sanujkul/KALAM_Canast_2019/Old Git Repo/BAGS/Eagle/Container/Cansat2019_1516_Container_v02.brd

## EAGLE design Old Git Repo/BAGS/Eagle/Container/Cansat2019_1516_Container_v02.brd (2019-06-20, an earlier design)

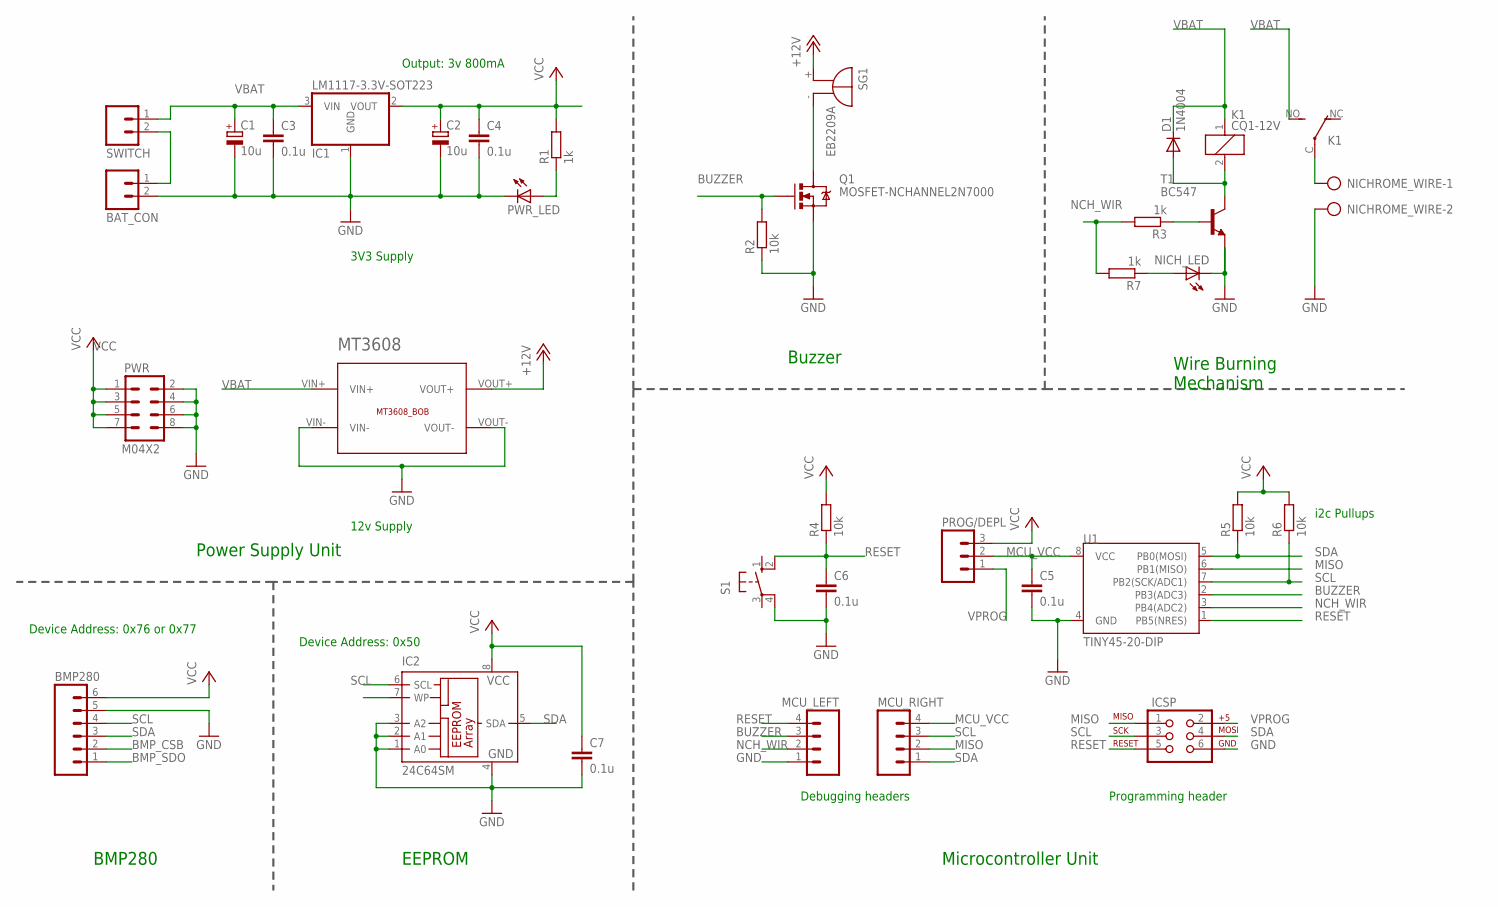
[picture p47: schematic Cansat2019_1516_Container_v02.sch]

Parts:
BAT_CON: M02; 02P
BMP280: M06; 06P
C1, C2: 10u; E2,5-6
C3, C4, C5, C6, C7: 0.1u; C025-025X050
D1: 1N4004; DO41-10
IC1: LM1117-3.3V-SOT223; SOT223
IC2: 24C64SM; SO-08M
ICSP: AVR_SPI_PRG_6NS; 2X3-NS
K1: CQ1-12V; CQ1
MCU_LEFT: M04; 04P
MCU_RIGHT: M04; 04P
MT3608: MT3608_BOB
NICHROME_WIRE: AK500/2-H
NICH_LED: LED3MM
PROG/DEPL: M03PTH; 1X03
PWR: M04X2; 2X4
PWR_LED: LED3MM
Q1: MOSFET-NCHANNEL2N7000; TO-92
R1, R3, R7: 1k; 0204/7
R2, R4, R5, R6: 10k; 0204/7
S1: PUSH-BUTTON-6MM; B3F-10XX
SG1: EB2209A
SWITCH: M02; 02P
T1: BC547; TO92
U1: TINY45-20-DIP; DIP08

Connections:
+12V: MT3608.VOUT+, SG1.+
BMP_CSB: BMP280.2
BMP_SDO: BMP280.1
BUZZER: MCU_LEFT.3, Q1.2 (G), R2.2, U1.2 (PB3(ADC3))
GND: BAT_CON.2, BMP280.5, C1.-, C2.-, C3.2, C4.2, C5.2, C6.2, C7.2, IC1.1 (GND), IC2.1 (A0), IC2.2 (A1), IC2.3 (A2), IC2.4 (GND), ICSP.6, MCU_LEFT.1, MT3608.VIN-, MT3608.VOUT-, NICHROME_WIRE.2, NICH_LED.K (C), PWR.2, PWR.4, PWR.6, PWR.8, PWR_LED.K (C), Q1.1 (S), R2.1, S1.4 (P1), U1.4 (GND)
MCU_VCC: C5.1, MCU_RIGHT.4, PROG/DEPL.2, U1.8 (VCC)
MISO: ICSP.1, MCU_RIGHT.2, U1.6 (PB1(MISO))
unnamed: Q1.3 (D), SG1.-
unnamed: K1.C, NICHROME_WIRE.1
unnamed: PWR_LED.A, R1.1
unnamed: R3.1, T1.2 (B)
unnamed: NICH_LED.A, R7.1
unnamed: BAT_CON.1, SWITCH.2
unnamed: D1.A, K1.2, T1.3 (C)
NCH_WIR: MCU_LEFT.2, R3.2, R7.2, U1.3 (PB4(ADC2))
RESET: C6.1, ICSP.5, MCU_LEFT.4, R4.1, S1.2 (S1), U1.1 (PB5(NRES))
SCL: BMP280.4, IC2.6 (SCL), ICSP.3, MCU_RIGHT.3, R6.1, U1.7 (PB2(SCK/ADC1))
SDA: BMP280.3, IC2.5 (SDA), ICSP.4, MCU_RIGHT.1, R5.1, U1.5 (PB0(MOSI))
VBAT: C1.+, C3.1, D1.C, IC1.3 (VIN), K1.1, K1.NO (S), MT3608.VIN+, SWITCH.1
VCC: BMP280.6, C2.+, C4.1, C7.1, IC1.2 (VOUT), IC2.8 (VCC), PROG/DEPL.3, PWR.1, PWR.3, PWR.5, PWR.7, R1.2, R4.2, R5.2, R6.2
VPROG: ICSP.2, PROG/DEPL.1

Notes on the sheet:
Power Supply Unit
Buzzer
Wire Burning Mechanism
Debugging headers
Programming header
Microcontroller Unit
3V3 Supply
12v Supply
BMP280
i2c Pullups
Output: 3v 800mA
Device Address: 0x50
EEPROM
Device Address: 0x76 or 0x77
