sanujkul/KALAM_Canast_2019/Old Git Repo/BAGS/Eagle/Container/Cansat2019_1516_Container_v02.brd

## EAGLE design Old Git Repo/BAGS/Eagle/Container/Cansat2019_1516_Container_v02.brd (continued)

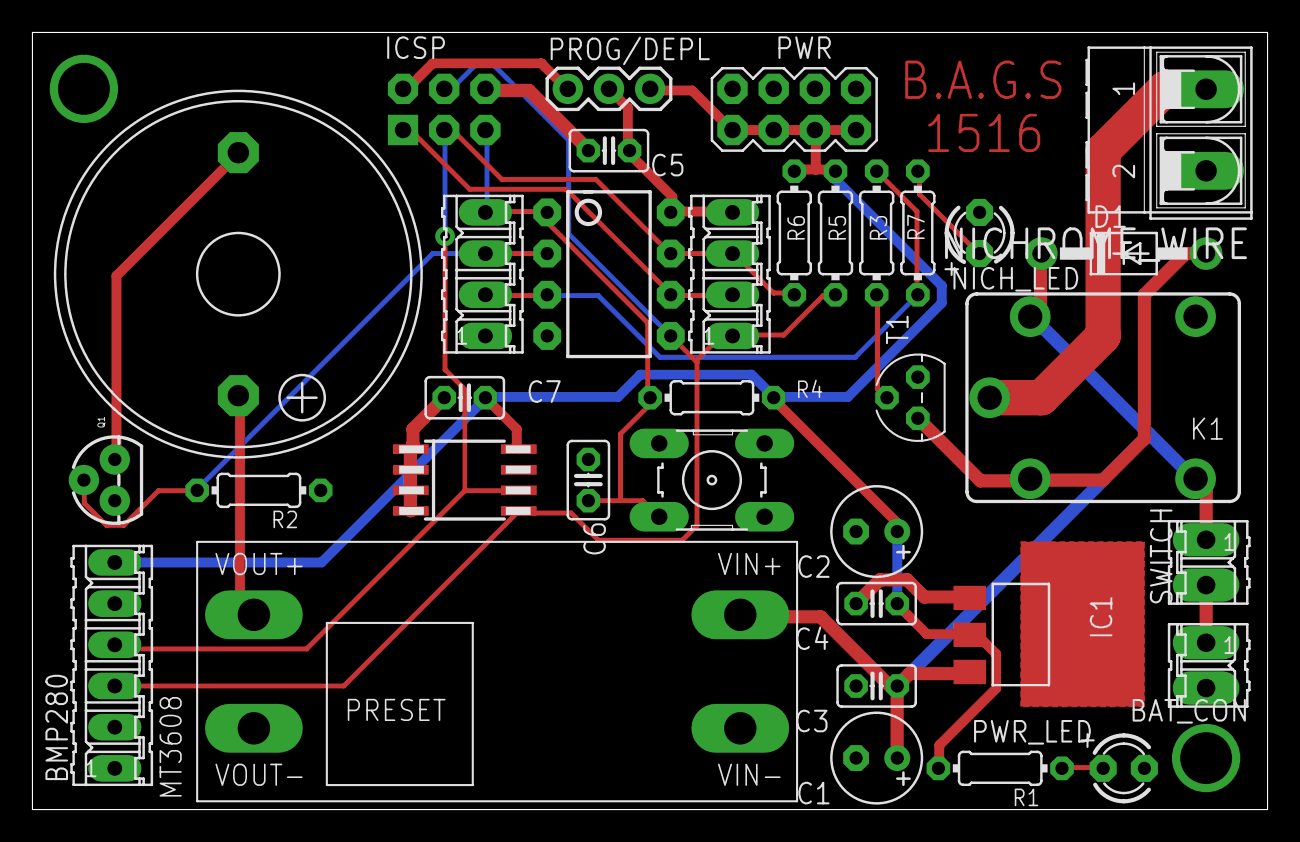
[picture p48: board Cansat2019_1516_Container_v02.brd from above]

Board: 2 copper layers, 76.2 x 47.9 mm, 35 parts (0 on the bottom side), 19 nets.
