sanujkul/KALAM_Canast_2019/Old Git Repo/KALAM/EAGLE/Container/Cansat2019_3279_Container_v03.brd

## EAGLE design Old Git Repo/KALAM/EAGLE/Container/Cansat2019_3279_Container_v03.brd (2019-06-20, an earlier design)

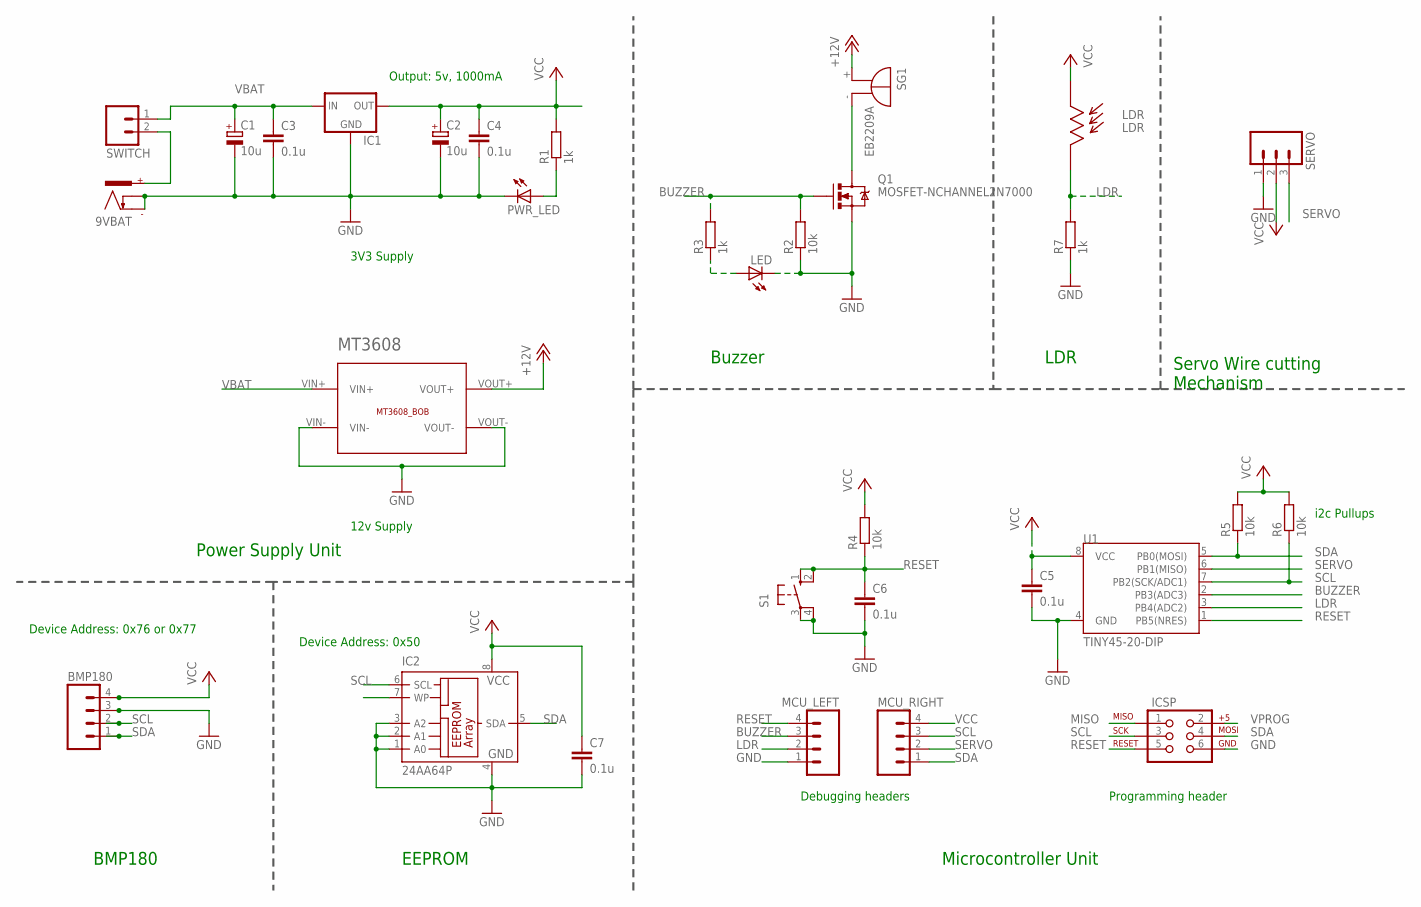
[picture p49: schematic Cansat2019_3279_Container_v03.sch]

Parts:
9VBAT: POWER_CON; NEB21R
BMP180: M04; 04P
C1, C2: 10u; E2,5-6
C3, C4, C5, C6, C7: 0.1u; C025-025X050
IC1: V_REG_78XX-TO-220; TO-220-ALT
IC2: 24AA64P; DIL8
ICSP: AVR_SPI_PRG_6NS; 2X3-NS
LDR: LDR; LDR-5MM
LED: LED3MM
MCU_LEFT: M04; 04P
MCU_RIGHT: M04; 04P
MT3608: MT3608_BOB
PWR_LED: LED3MM
Q1: MOSFET-NCHANNEL2N7000; TO-92
R1, R3, R7: 1k; 0204/7
R2, R4, R5, R6: 10k; 0204/7
S1: PUSH-BUTTON-6MM; B3F-10XX
SERVO: M03; 03P
SG1: EB2209A
SWITCH: M02; 02P
U1: TINY45-20-DIP; DIP08

Connections:
+12V: MT3608.VOUT+, SG1.+
BUZZER: MCU_LEFT.3, Q1.2 (G), R2.2, R3.2, U1.2 (PB3(ADC3))
GND: 9VBAT.-, 9VBAT.C, BMP180.3, C1.-, C2.-, C3.2, C4.2, C5.2, C6.2, C7.2, IC1.GND, IC2.1 (A0), IC2.2 (A1), IC2.3 (A2), IC2.4 (GND), ICSP.6, LED.K (C), MCU_LEFT.1, MT3608.VIN-, MT3608.VOUT-, PWR_LED.K (C), Q1.1 (S), R2.1, R7.1, S1.3, S1.4 (P1), SERVO.1, U1.4 (GND)
LDR: LDR.P$2, MCU_LEFT.2, R7.2, U1.3 (PB4(ADC2))
MISO: ICSP.1
unnamed: Q1.3 (D), SG1.-
unnamed: LED.A, R3.1
unnamed: PWR_LED.A, R1.1
unnamed: 9VBAT.+, SWITCH.2
RESET: C6.1, ICSP.5, MCU_LEFT.4, R4.1, S1.1 (S), S1.2 (S1), U1.1 (PB5(NRES))
SCL: BMP180.2, IC2.6 (SCL), ICSP.3, MCU_RIGHT.3, R6.1, U1.7 (PB2(SCK/ADC1))
SDA: BMP180.1, IC2.5 (SDA), ICSP.4, MCU_RIGHT.1, R5.1, U1.5 (PB0(MOSI))
SERVO: MCU_RIGHT.2, SERVO.3, U1.6 (PB1(MISO))
VBAT: C1.+, C3.1, IC1.IN, MT3608.VIN+, SWITCH.1
VCC: BMP180.4, C2.+, C4.1, C5.1, C7.1, IC1.OUT, IC2.8 (VCC), LDR.P$1, MCU_RIGHT.4, R1.2, R4.2, R5.2, R6.2, SERVO.2, U1.8 (VCC)
VPROG: ICSP.2

Notes on the sheet:
Power Supply Unit
Buzzer
Servo Wire cutting Mechanism
Debugging headers
Programming header
Microcontroller Unit
3V3 Supply
12v Supply
BMP180
i2c Pullups
Output: 5v, 1000mA
Device Address: 0x50
EEPROM
Device Address: 0x76 or 0x77
LDR

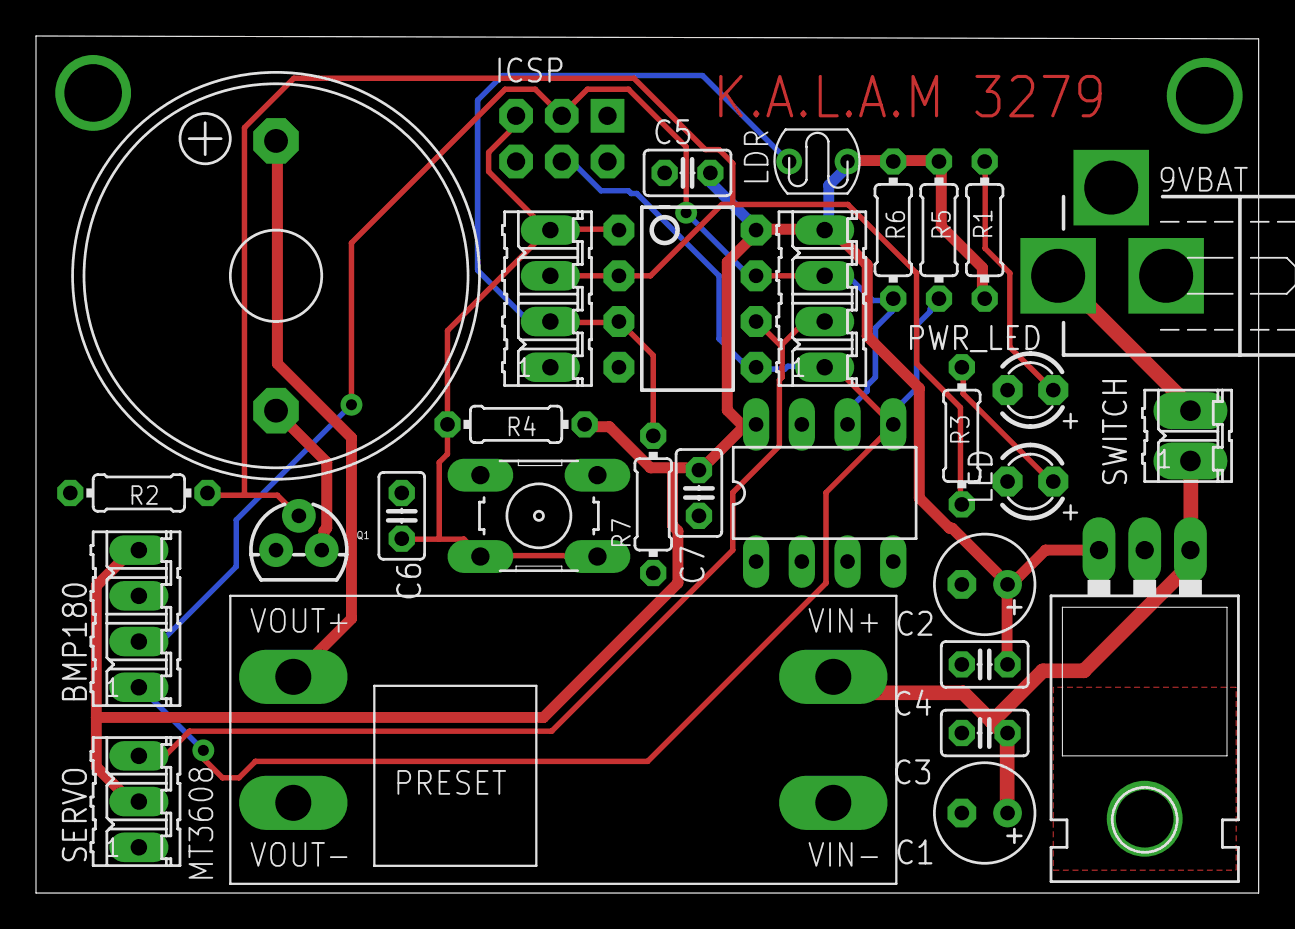
[picture p50: board Cansat2019_3279_Container_v03.brd from above]

Board: 2 copper layers, 67.9 x 47.6 mm, 31 parts (0 on the bottom side), 14 nets.
