sanujkul/KALAM_Canast_2019/Old Git Repo/KALAM/EAGLE/Container/Cansat2019_3279_Container_v04.brd

## EAGLE design Old Git Repo/KALAM/EAGLE/Container/Cansat2019_3279_Container_v04.brd (2019-06-20, an earlier design)

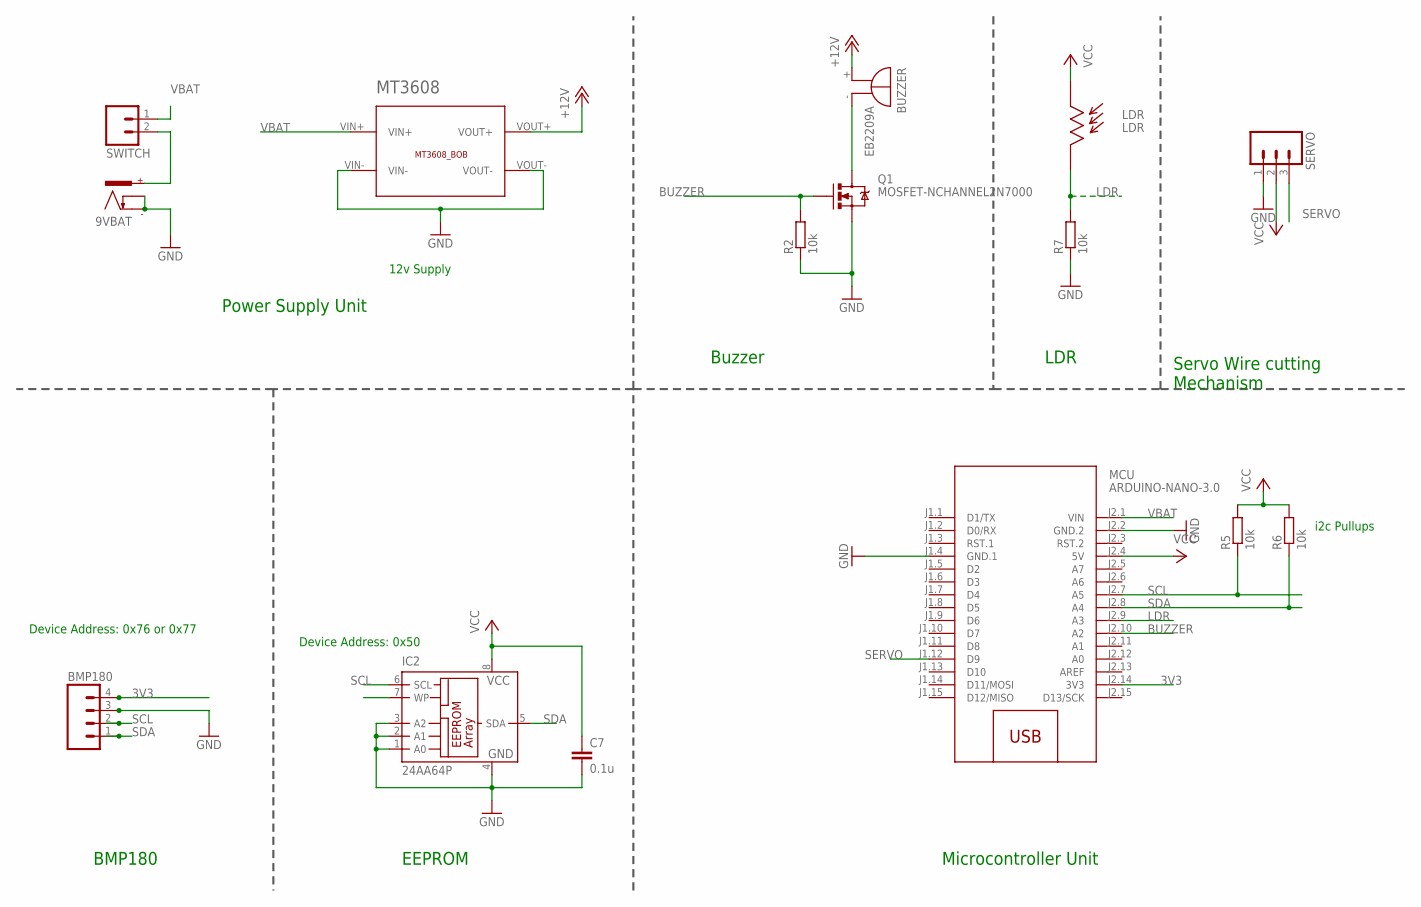
[picture p51: schematic Cansat2019_3279_Container_v04.sch]

Parts:
9VBAT: POWER_CON; NEB21R
BMP180: M04; 04P
BUZZER: EB2209A
C7: 0.1u; C025-025X050
IC2: 24AA64P; DIL8
LDR: LDR; LDR-5MM
MCU: ARDUINO-NANO-3.0
MT3608: MT3608_BOB
Q1: MOSFET-NCHANNEL2N7000; TO-92
R2, R5, R6, R7: 10k; 0204/7
SERVO: M03; 03P
SWITCH: M02; 02P

Connections:
3V3: BMP180.4, MCU.J2.14 (3V3)
+12V: BUZZER.+, MT3608.VOUT+
BUZZER: MCU.J2.10 (A2), Q1.2 (G), R2.2
GND: 9VBAT.-, 9VBAT.C, BMP180.3, C7.2, IC2.1 (A0), IC2.2 (A1), IC2.3 (A2), IC2.4 (GND), MCU.J1.4 (GND.1), MCU.J2.2 (GND.2), MT3608.VIN-, MT3608.VOUT-, Q1.1 (S), R2.1, R7.1, SERVO.1
LDR: LDR.P$2, MCU.J2.9 (A3), R7.2
unnamed: BUZZER.-, Q1.3 (D)
unnamed: 9VBAT.+, SWITCH.2
SCL: BMP180.2, IC2.6 (SCL), MCU.J2.7 (A5), R5.1
SDA: BMP180.1, IC2.5 (SDA), MCU.J2.8 (A4), R6.1
SERVO: MCU.J1.12 (D9), SERVO.3
VBAT: MCU.J2.1 (VIN), MT3608.VIN+, SWITCH.1
VCC: C7.1, IC2.8 (VCC), LDR.P$1, MCU.J2.4 (5V), R5.2, R6.2, SERVO.2

Notes on the sheet:
Power Supply Unit
Buzzer
Servo Wire cutting Mechanism
Microcontroller Unit
12v Supply
BMP180
i2c Pullups
Device Address: 0x50
EEPROM
Device Address: 0x76 or 0x77
LDR

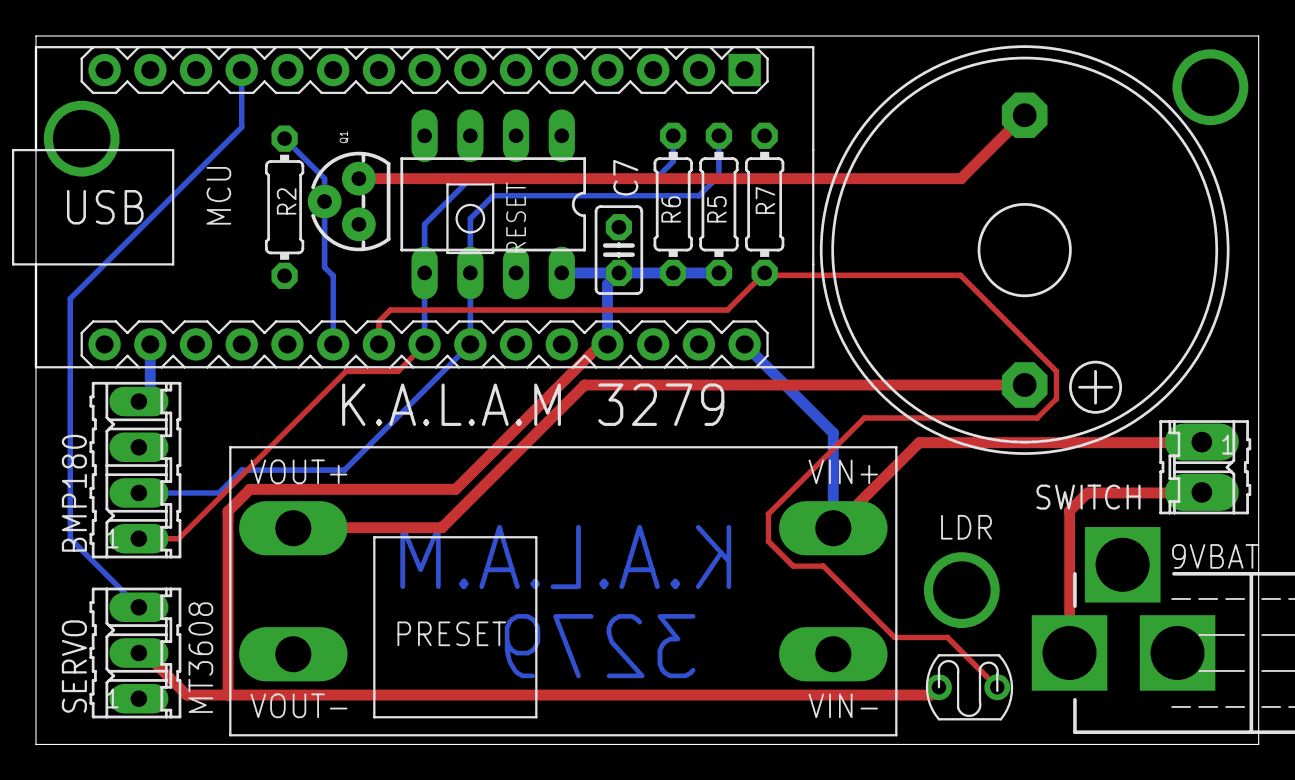
[picture p52: board Cansat2019_3279_Container_v04.brd from above]

Board: 2 copper layers, 67.9 x 39.4 mm, 15 parts (0 on the bottom side), 12 nets.
