sanujkul/KALAM_Canast_2019/Old Git Repo/KALAM/EAGLE/Container/Cansat2019_3279_Container_v05.brd

## EAGLE design Old Git Repo/KALAM/EAGLE/Container/Cansat2019_3279_Container_v05.brd (2019-06-20, an earlier design)

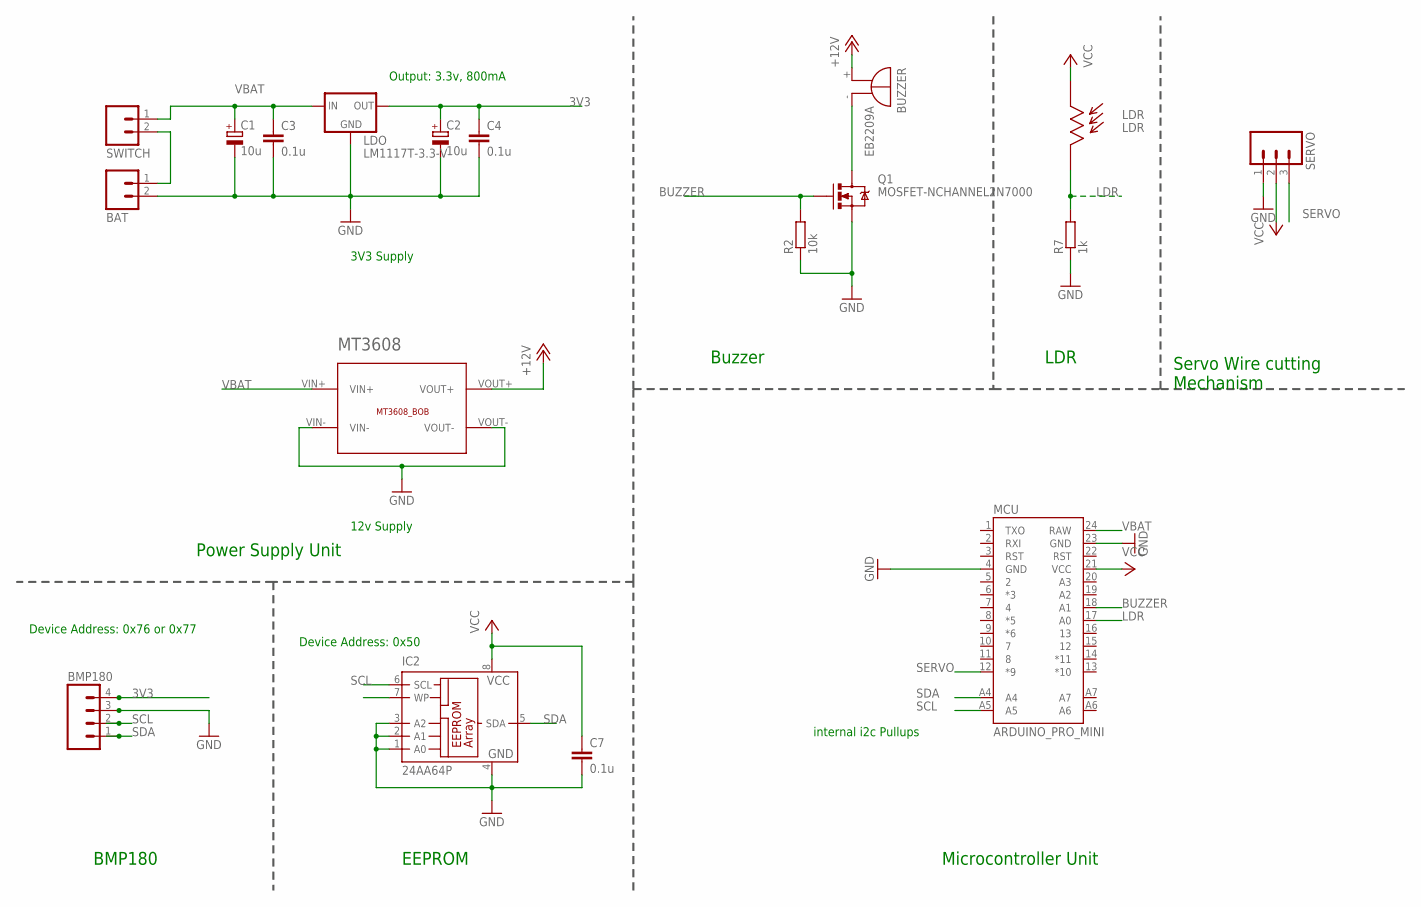
[picture p53: schematic Cansat2019_3279_Container_v05.sch]

Parts:
BAT: M02; 02P
BMP180: M04; 04P
BUZZER: EB2209A
C1, C2: 10u; E2,5-6
C3, C4, C7: 0.1u; C025-025X050
IC2: 24AA64P; DIL8
LDO: LM1117T-3.3-V; TO220V
LDR: LDR; LDR-5MM
MCU: ARDUINO_PRO_MINI
MT3608: MT3608_BOB
Q1: MOSFET-NCHANNEL2N7000; TO-92
R2: 10k; 0204/7
R7: 1k; 0204/7
SERVO: M03; 03P
SWITCH: M02; 02P

Connections:
3V3: BMP180.4, C2.+, C4.1, LDO.2 (OUT)
+12V: BUZZER.+, MT3608.VOUT+
BUZZER: MCU.18 (A1), Q1.2 (G), R2.2
GND: BAT.2, BMP180.3, C1.-, C2.-, C3.2, C4.2, C7.2, IC2.1 (A0), IC2.2 (A1), IC2.3 (A2), IC2.4 (GND), LDO.1 (GND), MCU.4 (GND), MCU.23 (GND), MT3608.VIN-, MT3608.VOUT-, Q1.1 (S), R2.1, R7.1, SERVO.1
LDR: LDR.P$2, MCU.17 (A0), R7.2
unnamed: BUZZER.-, Q1.3 (D)
unnamed: BAT.1, SWITCH.2
SCL: BMP180.2, IC2.6 (SCL), MCU.A5
SDA: BMP180.1, IC2.5 (SDA), MCU.A4
SERVO: MCU.12 (*9), SERVO.3
VBAT: C1.+, C3.1, LDO.3 (IN), MCU.24 (RAW), MT3608.VIN+, SWITCH.1
VCC: C7.1, IC2.8 (VCC), LDR.P$1, MCU.21 (VCC), SERVO.2

Notes on the sheet:
Power Supply Unit
Buzzer
Servo Wire cutting Mechanism
Microcontroller Unit
3V3 Supply
12v Supply
BMP180
Output: 3.3v, 800mA
Device Address: 0x50
EEPROM
Device Address: 0x76 or 0x77
LDR
internal i2c Pullups

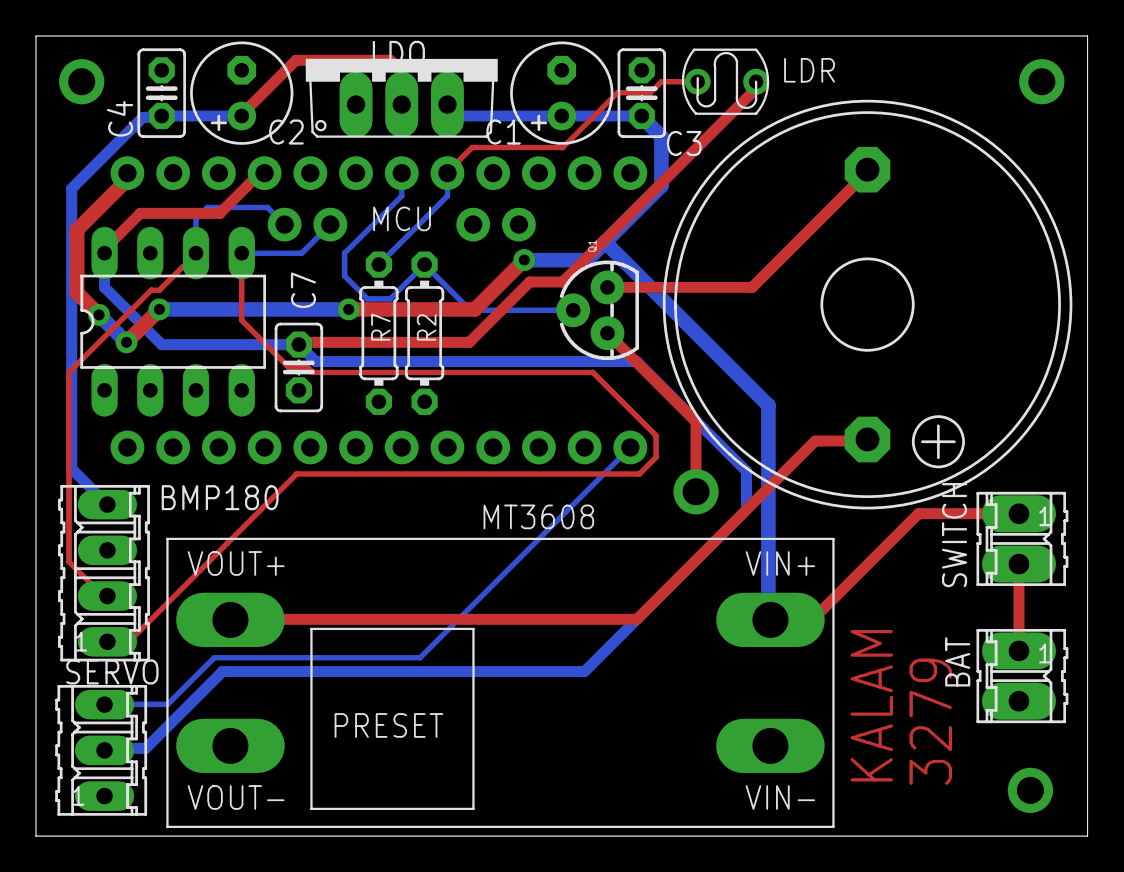
[picture p54: board Cansat2019_3279_Container_v05.brd from above]

Board: 2 copper layers, 58.4 x 44.5 mm, 18 parts (0 on the bottom side), 12 nets.
