sanujkul/KALAM_Canast_2019/Old Git Repo/KALAM/EAGLE/Payload_SectionA/PayloadV4.brd

## EAGLE design Old Git Repo/KALAM/EAGLE/Payload_SectionA/PayloadV4.brd (2019-06-20, an earlier design)

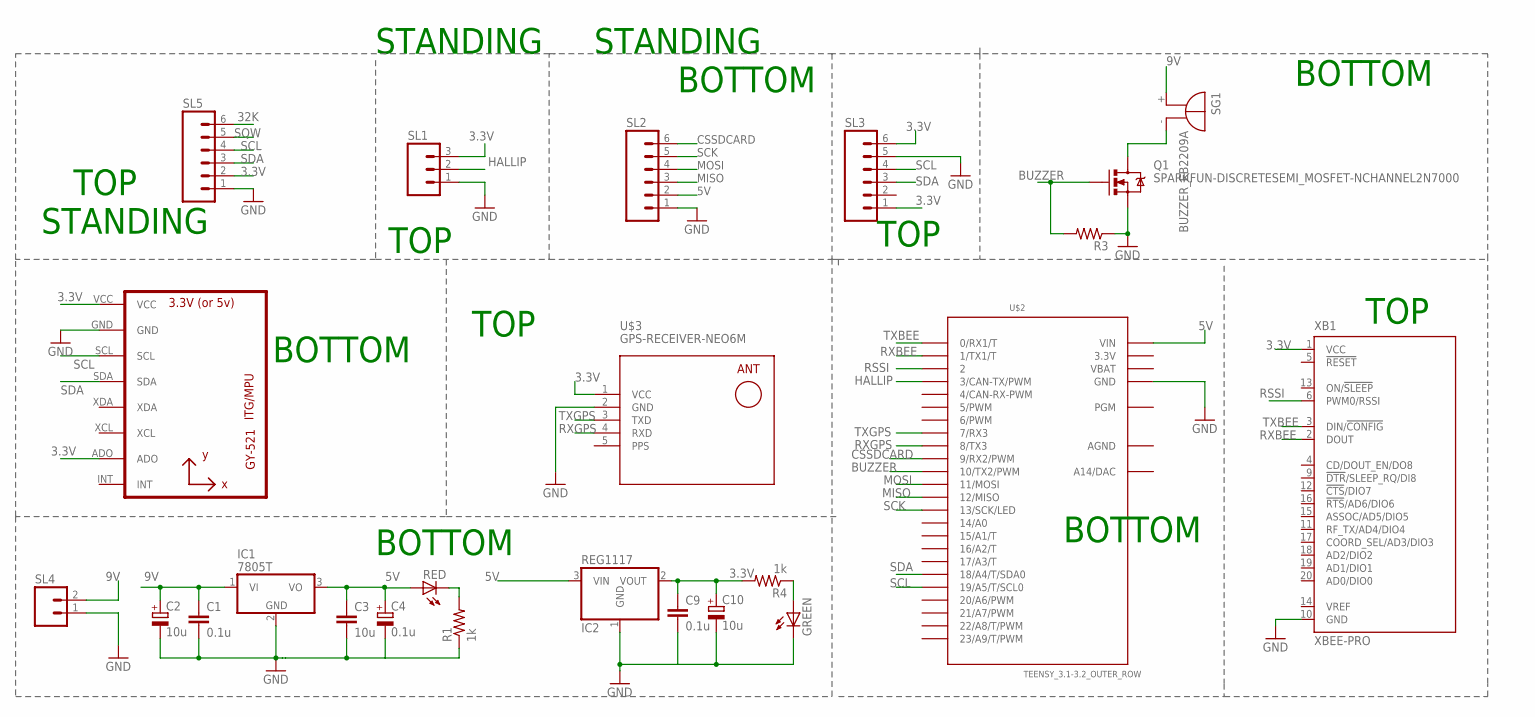
[picture p55: schematic PayloadV4.sch]

Parts:
C1, C9: 0.1u; C025-025X050
C2, C10: 10u; E2,5-6
C3: 10u; C025-025X050
C4: 0.1u; E2,5-6
GREEN: red; LED3MM
IC1: 7805T; TO220H
IC2: REG1117; SOT223
Q1: SPARKFUN-DISCRETESEMI_MOSFET-NCHANNEL2N7000; SPARKFUN-DISCRETESEMI_TO-92
R1, R4: 1k; 0204/7
R3: R-US_0204/7; 0204/7
RED: red; LED3MM
SG1: BUZZER_EB2209A
SL1: M03; 03P
SL2, SL3, SL5: M06; 06P
SL4: M02; 02P
U1: GY-521MPU6050; GY-521
U$2: TEENSY_3.1-3.2_OUTER_ROW; TEENSY_3.0-3.2&LC_OUTER_ROW
U$3: GPS-RECEIVER-NEO6M
XB1: XBEE-PRO

Connections:
3.3V: C9.1, C10.+, IC2.2 (VOUT), R4.2, SL1.3, SL3.1, SL3.6, SL5.2, U1.ADO, U1.VCC, U$2.3.3V, U$2.3.3V1 (3.3V), U$3.1 (VCC), XB1.1 (VCC)
5V: C3.1, C4.+, IC1.3 (VO), IC2.3 (VIN), RED.A, SL2.2, U$2.VIN
9V: C1.1, C2.+, IC1.1 (VI), SG1.+, SL4.2
32K: SL5.6
AGND: U$2.AGND
BUZZER: Q1.2 (G), R3.2, U$2.10 (10/TX2/PWM)
CSSDCARD: SL2.6, U$2.9 (9/RX2/PWM)
GND: C1.2, C2.-, C3.2, C4.-, C9.2, C10.-, GREEN.K (C), IC1.2 (GND), IC2.1 (GND), Q1.1 (S), R1.1, R3.1, SL1.1, SL2.1, SL3.5, SL4.1, SL5.1, U1.GND, U$2.GND, U$2.GND1 (GND), U$3.2 (GND), XB1.10 (GND)
HALLIP: SL1.2, U$2.3 (3/CAN-TX/PWM)
MISO: SL2.3, U$2.12 (12/MISO)
MOSI: SL2.4, U$2.11 (11/MOSI)
unnamed: R1.2, RED.K (C)
unnamed: GREEN.A, R4.1
unnamed: Q1.3 (D), SG1.-
PPS: U$3.5 (PPS)
RSSI: U$2.2, XB1.6 (PWM0/RSSI)
RXBEE: U$2.1 (1/TX1/T), XB1.2 (DOUT)
RXGPS: U$2.8 (8/TX3), U$3.4 (RXD)
SCK: SL2.5, U$2.13 (13/SCK/LED)
SCL: SL3.4, SL5.4, U1.SCL, U$2.19/A5 (19/A5/T/SCL0)
SDA: SL3.3, SL5.3, U1.SDA, U$2.18/A4 (18/A4/T/SDA0)
SQW: SL5.5
TXBEE: U$2.0 (0/RX1/T), XB1.3 (DIN/!CONFIG)
TXGPS: U$2.7 (7/RX3), U$3.3 (TXD)
VBAT: U$2.VBAT

Notes on the sheet:
TOP
BOTTOM
STANDING

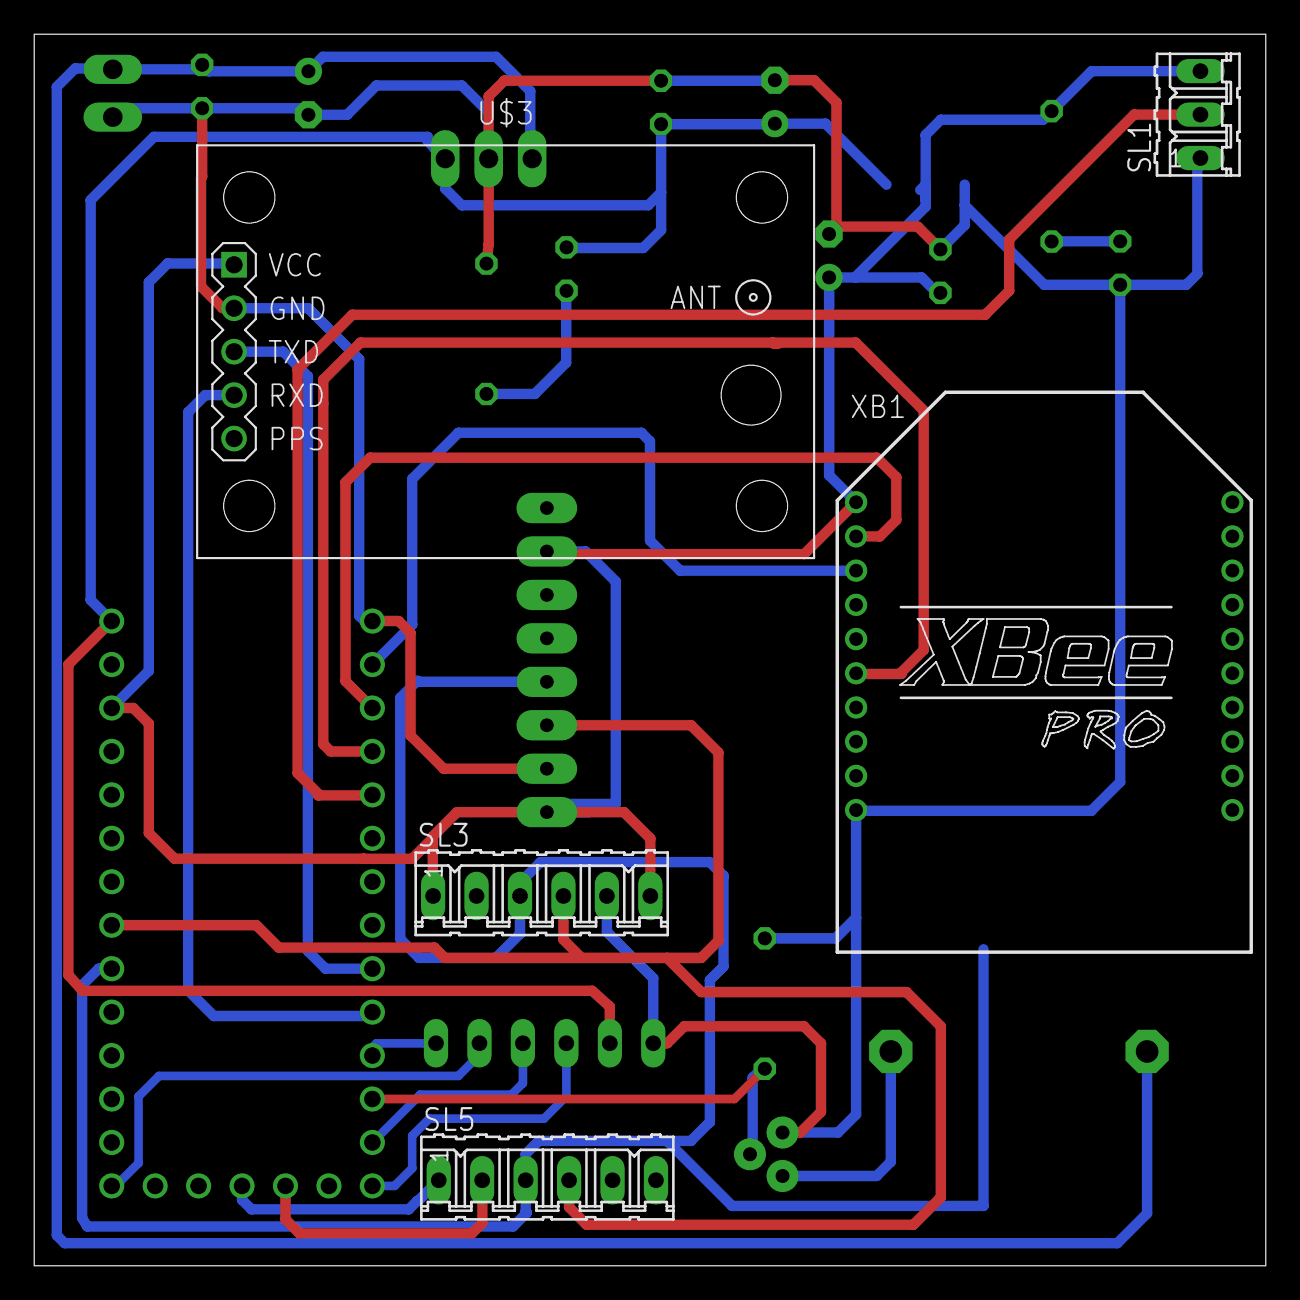
[picture p56: board PayloadV4.brd from above]

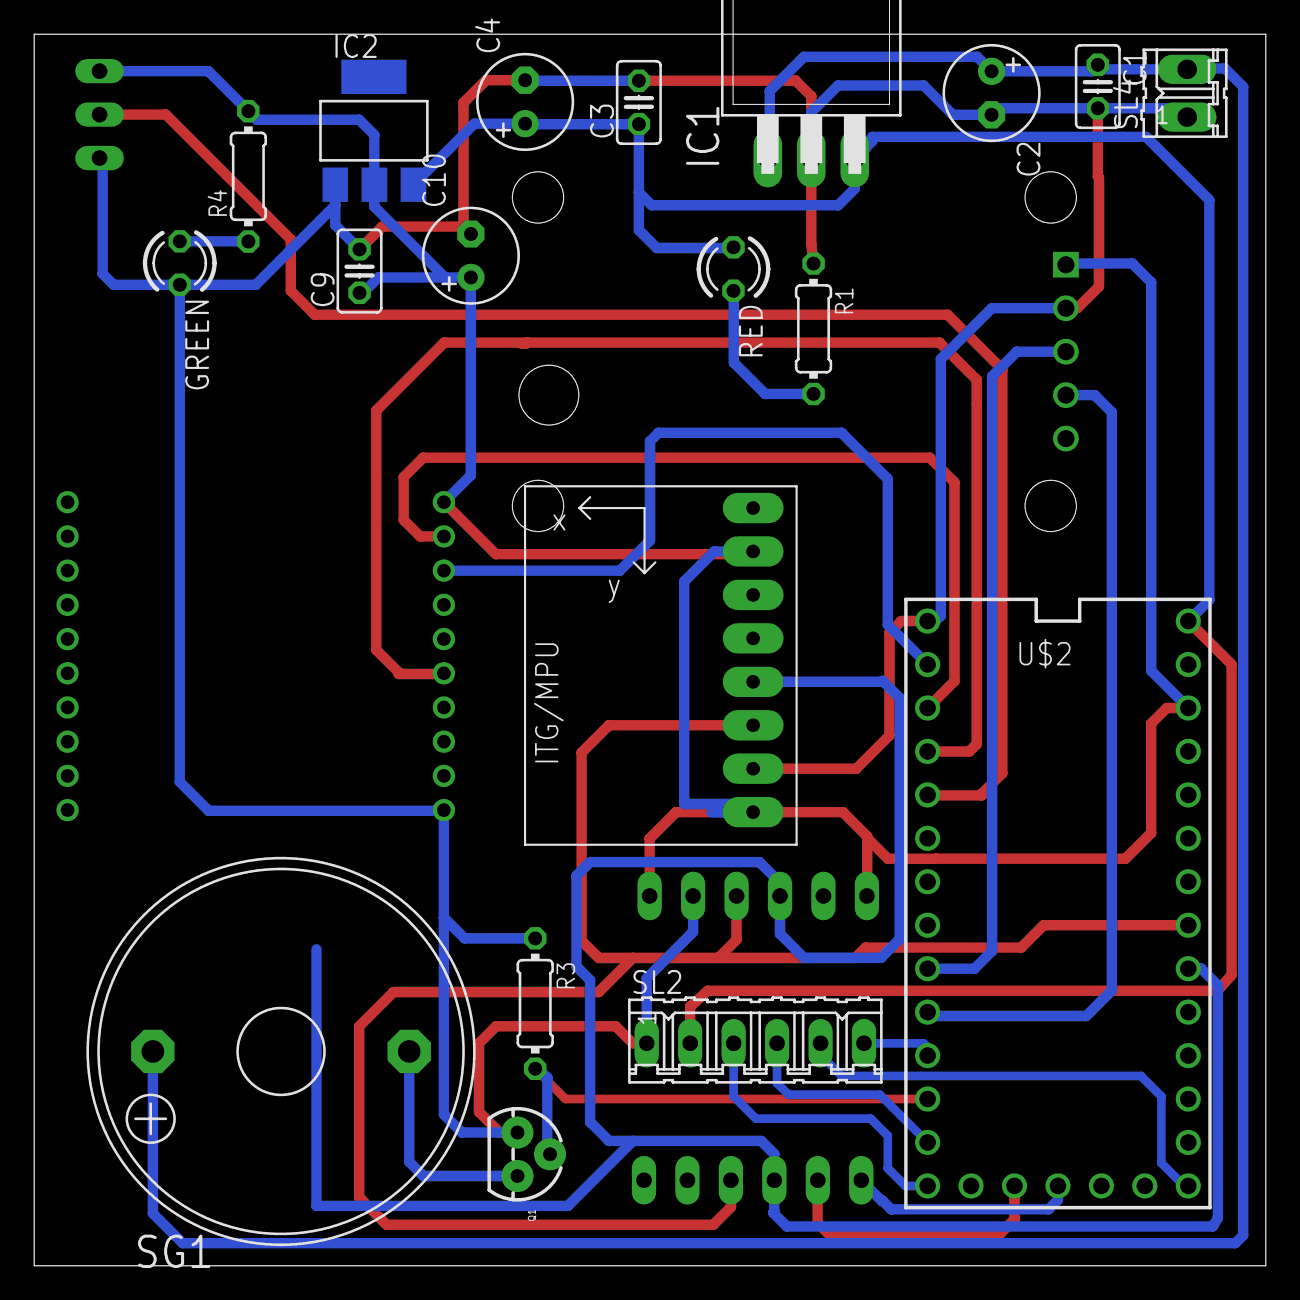
[picture p57: board PayloadV4.brd from below]

Board: 2 copper layers, 72.0 x 72.0 mm, 24 parts (19 on the bottom side), 20 nets.
