sanujkul/KALAM_Canast_2019/TeensyPayloadCodes/TEENSY_Prototype4/b_bmp.ino

volatile float ground_altitude = 0;

void initBmp(){
  if (!bmp.begin()) {
		#ifdef SER_DEBUG
			Serial.println(F("Could not find a valid BMP280 sensor, check wiring!"));
		#endif

      xbee.println("Could not find a valid BMP280 sensor, check wiring!");
      return;
	}
  /* Default settings from datasheet. */
  bmp.setSampling(Adafruit_BMP280::MODE_NORMAL,     /* Operating Mode. */
                  Adafruit_BMP280::SAMPLING_X2,     /* Temp. oversampling */
                  Adafruit_BMP280::SAMPLING_X16,    /* Pressure oversampling */
                  Adafruit_BMP280::FILTER_OFF,      /* Filtering. */
                  Adafruit_BMP280::STANDBY_MS_500); /* Standby time. */	

               
}

void setGroundAltitude(){
  double sum = 0;
  for(int i=0; i<2000; i++){
    sum += bmp.readAltitude(1013.25);
  }
  ground_altitude = sum/2000;
}

void setGroundAltitude(float alt){
  ground_altitude = alt;
}

volatile float getBMPAltitute(){
  return (bmp.readAltitude(1013.25) - ground_altitude);
}


//void setup() {
//  Serial.begin(115200);
//	Serial.println("Begin");
//  Wire1.begin();
//  //I2C
//  pinPeripheral(SDA, PIO_SERCOM_ALT);
//  pinPeripheral(SCL, PIO_SERCOM_ALT);
//  
//  Serial.println(F("BMP280 test"));
//
//  if (!bmp.begin()) {
//    Serial.println(F("Could not find a valid BMP280 sensor, check wiring!"));
//    while (1);
//  }
//
//  /* Default settings from datasheet. */
//  bmp.setSampling(Adafruit_BMP280::MODE_NORMAL,     /* Operating Mode. */
//                  Adafruit_BMP280::SAMPLING_X2,     /* Temp. oversampling */
//                  Adafruit_BMP280::SAMPLING_X16,    /* Pressure oversampling */
//                  Adafruit_BMP280::FILTER_X16,      /* Filtering. */
//                  Adafruit_BMP280::STANDBY_MS_500); /* Standby time. */
//}
//
//void loop() {
//    Serial.print(F("Temperature = "));
//    Serial.print(bmp.readTemperature());
//    Serial.println(" *C");
//
//    Serial.print(F("Pressure = "));
//    Serial.print(bmp.readPressure());
//    Serial.println(" Pa");
//
//    Serial.print(F("Approx altitude = "));
//    Serial.print(bmp.readAltitude(1013.25)); /* Adjusted to local forecast! */
//    Serial.println(" m");
//
//    Serial.println();
//    delay(2000);
//}
